dSZfAjvn/stm32h743_cam/CUBEMX/Inc/bmp.h

#ifndef _FF_INTEGER
typedef unsigned short DWORD; //4bytes
typedef unsigned long LONG;   //4bytes
#endif

typedef unsigned short WORD;   //2bytes
typedef unsigned char BYTE;    

#pragma pack(2)
typedef struct tagBITMAPFILEHEADER  //bmp�ļ�ͷ
{
	WORD bfType; // ???????,???BM
	DWORD bfSize;	 // ???????,??????
	WORD bfReserved1; // ???????,???0
	WORD bfReserved2; // ???????,???0
	DWORD bfOffBits; // ?????????,??????
}BITMAPFILEHEADER;
	
	
typedef struct tagBITMAPINFOHEADER{  //λͼ��Ϣͷ
	
	DWORD biSize; // ?????????
	LONG biWidth; // ?????,??????
	LONG biHeight; // ?????,??????
	WORD biPlanes; // ???????,???1
	WORD biBitCount;// ?????????,???1(??),
	// 4(16?),8(256?)?24(???)??
	DWORD biCompression; // ??????,??? 0(???),
	// 1(BI_RLE8????)?2(BI_RLE4????)??
	DWORD biSizeImage; // ?????,??????
	LONG biXPelsPerMeter; // ???????,?????
	LONG biYPelsPerMeter; // ???????,?????
	DWORD biClrUsed;// ???????????????
	DWORD biClrImportant;// ?????????????
}BITMAPINFOHEADER;
	

typedef struct tagPIXEL  //λͼ��Ϣͷ
{
	WORD COLOR;
}PIXEL;


typedef struct tagBMP  //λͼ��Ϣͷ
{
	BITMAPFILEHEADER bitmapfileheader;
	BITMAPINFOHEADER bitmapinfoheader;
	unsigned short *pixel;
}BMP;
#pragma pack()
